tstrade/Drone-Companion/FinalProduct/DroneCompanionFullWiring.png

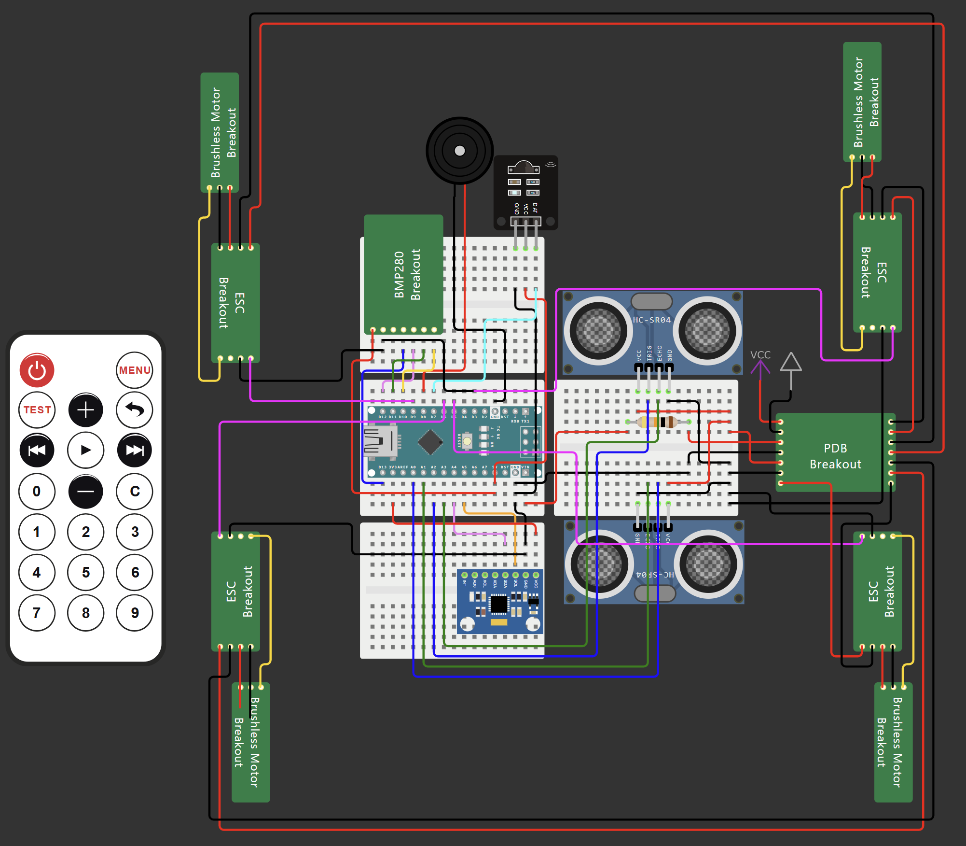
FinalProduct/DroneCompanionFullWiring.png
