tstrade/Drone-Companion/Software/Test Code/GyroAccelTest/GyroAccelTest_WIP/GyroAccelTest_WIP.ino

#include <MPU6050.h>
#include <Wire.h>

MPU6050 mpu;

// Timers
unsigned long timer = 0;
float timeStep = 0.01;

// Pitch, Roll and Yaw values
float pitch = 0;
float roll = 0;
float yaw = 0;

void setup() {
  Serial.begin(115200);

  Serial.println("Initialize MPU6050");
  while (!mpu.begin(MPU6050_SCALE_2000DPS, MPU6050_RANGE_2G)) {
    Serial.println("Failed to find MPU6050 chip, checking wiring!");
    delay(500);
  }

  mpu.calibrateGyro();
  mpu.setThreshold(3);
}

void loop() {
  timer = millis();

  // Read normalized values
  Vector norm = mpu.readNormalizeGyro();

  // Calculate Pitch, Roll and Yaw
  pitch = pitch + norm.YAxis * timeStep;
  roll = roll + norm.XAxis * timeStep;
  yaw = yaw + norm.ZAxis * timeStep;

  // Output raw
  Serial.print(" Pitch = ");
  Serial.print(pitch);
  Serial.print(" Roll = ");
  Serial.print(roll);  
  Serial.print(" Yaw = ");
  Serial.println(yaw);

  // Wait to full timeStep period
  delay((timeStep*1000) - (millis() - timer));
}
